BoujeeEnjinia1701/dustbadge/cad/drawings/DBG-DWG-001.pdf

CONCEPT, NOT FOR FABRICATION | DustBadge · github.com/BoujeeEnjinia1701/dustbadge

FRONT VIEW
Scale 1:1; looking at the front (along +Y)

TOP VIEW
Scale 1:1; looking down (along -Z)

RIGHT VIEW
Scale 1:1; looking at the right side (along -X)

64

35 52

6 ALERT LED LIGHT PIPE

5 MOTOR (HIDDEN)

3 SENSOR 41 x 41 x 12 (HIDDEN)

INLET | OUTLET

FRONT FACE (-Y), WORN FACING OUT

31
SHELL JOINT, GASKET

10 CLIP

AIR IN (DOWN)

ISOMETRIC VIEW
Not to scale; seen from the front right and above, about 30 deg elevation

MAIN DIMENSIONS AND INTERFACES (MM)
Shells 64 x 52 x 31; 35 deep with clip; wall 2; gasket 1 at 15 from the rear face Sensor SPS30 class 41 x 41 x 12, ports down onto two slots
Slots 12 x 7: inlet (screened) at X -19, outlet at X 1
USB-C opening at X 18; humidity vent at X 18; all in the bottom face
Cell 50 x 34 x 11.5, 2,000 mAh, protected, with thermistor; 13 foam pad 40 x 24 x 1 behind it Board 59 x 47 clamped by three M2 x 20 screws; TPU gasket and port seals
Mass 120.7 g (DBG-CAL-001); inlet 242 from nose and mouth when worn
Not intrinsically safe; not for gassy mines or explosive atmospheres
Wear shaded when ambient is above 40 °C in full sun
Third-angle; front view from -Y; origin at the badge center, rear face Y = 1
REV | DESCRIPTION | DATE | BY
P1 | Preliminary GA for TRL 3 (from cad/src/model.py) | 2026-09-25 | AC
P2 | 2,000 mAh cell, 11.5 thick; sun use rule (DBG-DDR-002) | 2026-09-25 | AC
P3 | Layout and labels tidied | 2026-09-25 | AC
P4 | Design for construction: screws, gasket, seals, ribs (DBG-DDR-003) | 2026-09-30 | AC
P5 | Worn version: rear 1 mm deeper, foam pad (DDR-003 A1) | 2026-10-02 | AC
DUSTBADGE | github.com/BoujeeEnjinia1701/dustbadge

## General arrangement

DRAWING NO.
DBG-DWG-001

REV
P5

SHEET
1 of 1

SIZE

## ANSI B

SCALE
1:1

UNITS
mm
PROJECTION | DATE
2026-10-02

DRAWN
Amish Chadha

MATERIAL / NOTES
PETG shells; bought-in parts per bom/bom.csv. PRELIMINARY, NOT FOR FABRICATION
Licensed CERN-OHL-S-2.0 · Design Molecule Lab · designmolecule.com | Generated from cad/src; do not edit by hand
