BoujeeEnjinia1701/dustbadge/cad/drawings/DBG-DWG-101.pdf

### BUILD PLAN SKETCH, PLAN NOT YET BUILT DustBadge · github.com/BoujeeEnjinia1701/dustbadge

FRONT VIEW
Scale 1:1; looking at the front (along +Y)

TOP VIEW
Scale 1:1; looking down (along -Z)

RIGHT VIEW
Scale 1:1; looking at the right side (along -X)

64

16 52

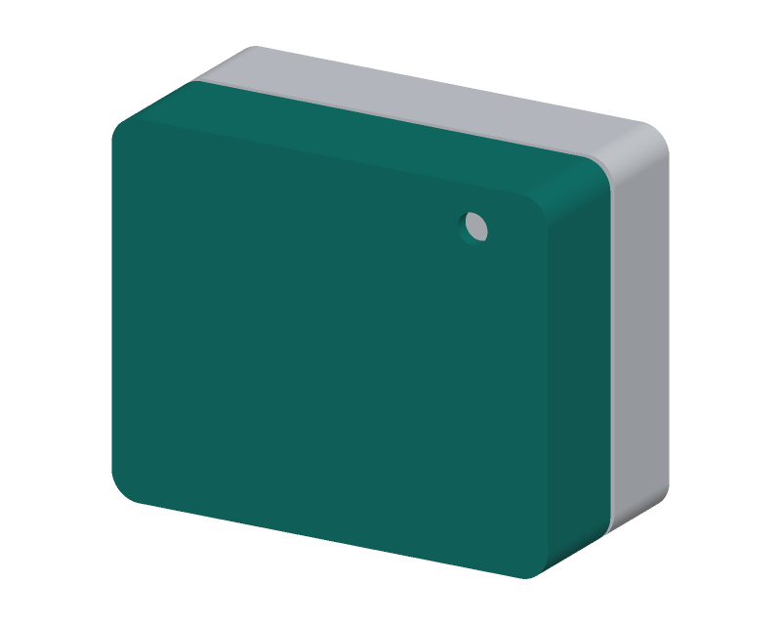
[picture p8: figure]

WHERE IT GOES
This part in colour, its neighbours in grey

HOW TO MAKE IT AND HOW IT FITS
Print face down (the front face on the bed); no supports needed. 64 x 52 x 16 mm, walls 2 mm, outside edges round 4 mm.
Bottom face openings (sideways from the centre line, + to the right seen from the front; depth from the front face):
inlet slot 12 x 7 at 19 left, outlet slot 12 x 7 at 1 right,
both 4.7 to 11.7 back; USB-C 9.6 x 3.8 at 18 right, 12.2 back; humidity vent 3 x 2 at 18.5 right, 2 to 4 back.
Light pipe hole 4.4 through the front face, 21 right, 20 above centre. Three screw bosses 5 dia, 14.2 long from the front face, at 27 left and 27 right 21 up, and 27 right 21 down: pilot hole 1.7 mm, 11 deep. Two stop ribs 1.2 thick above the sensor, 20 left and 2 right,
7 deep from the front face, their lower edge 0.2 above the sensor. Check: the sensor drops in under the ribs; the slots are clear.
REV | DESCRIPTION | DATE | BY
P1 | Making sketch for the prototype build plan | 2026-09-30 | AC
DUSTBADGE | github.com/BoujeeEnjinia1701/dustbadge

## DustBadge front shell: making sketch

DRAWING NO.
DBG-DWG-101

REV
P1

SHEET
1 of 1

SIZE

## ANSI B

SCALE
1:1

UNITS
mm
PROJECTION | DATE
2026-09-30

DRAWN
Amish Chadha

MATERIAL / NOTES
PETG, high-visibility yellow, 3D printed, 0.2 mm layers, 4 walls
Licensed CERN-OHL-S-2.0 · Design Molecule Lab · designmolecule.com | Generated from cad/src; do not edit by hand
