BoujeeEnjinia1701/dustbadge/cad/drawings/DBG-DWG-102.pdf

### BUILD PLAN SKETCH, PLAN NOT YET BUILT DustBadge · github.com/BoujeeEnjinia1701/dustbadge

FRONT VIEW
Scale 1:1; looking at the front (along +Y)

TOP VIEW
Scale 1:1; looking down (along -Z)

RIGHT VIEW
Scale 1:1; looking at the right side (along -X)

64

15 52

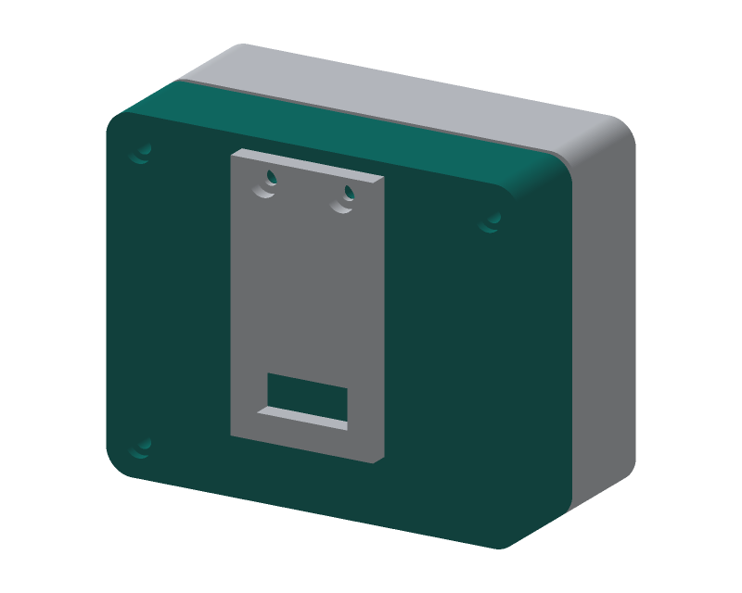
[picture p9: figure]

WHERE IT GOES
This part in colour, its neighbours in grey

HOW TO MAKE IT AND HOW IT FITS
Print rear face down; no supports needed.
64 x 52 x 14 mm, walls 2 mm, outside edges round 4 mm. Three tubes 4.5 dia, from the rear wall to 15.2 from the rear face, at the same places as the front bosses (seen from the front:
27 left and 27 right 21 up, 27 right 21 down); hole 2.4 through. Counterbore each from the rear face 4.2 dia, 1.4 deep (screw heads). Two clip bosses 5 dia, 5.5 long inside, 6 each side of centre,
21 up; pilot hole 1.7 mm, 7 deep from the rear face.
Four cell ribs 1.2 thick, 4 tall, 0.2 off the cell: two at the
sides (12 long), two at top and bottom (5 long).
Foam pad 40 x 24 x 1, stuck inside the back wall, centred. The rim is 14 from the rear face; the gasket sits on it. Check: the cell drops between the ribs and lifts out freely.
REV | DESCRIPTION | DATE | BY
P1 | Making sketch for the prototype build plan | 2026-09-30 | AC
DUSTBADGE | github.com/BoujeeEnjinia1701/dustbadge

## DustBadge rear shell: making sketch

DRAWING NO.
DBG-DWG-102

REV
P1

SHEET
1 of 1

SIZE

## ANSI B

SCALE
1:1

UNITS
mm
PROJECTION | DATE
2026-09-30

DRAWN
Amish Chadha

MATERIAL / NOTES
PETG, dark grey, 3D printed, 0.2 mm layers, 4 walls
Licensed CERN-OHL-S-2.0 · Design Molecule Lab · designmolecule.com | Generated from cad/src; do not edit by hand
