BoujeeEnjinia1701/dustbadge/cad/drawings/DBG-DWG-104.pdf

### BUILD PLAN SKETCH, PLAN NOT YET BUILT DustBadge · github.com/BoujeeEnjinia1701/dustbadge

FRONT VIEW
Scale 2:1; looking at the front (along +Y)

TOP VIEW
Scale 2:1; looking down (along -Z)

RIGHT VIEW
Scale 2:1; looking at the right side (along -X)

36

11 1

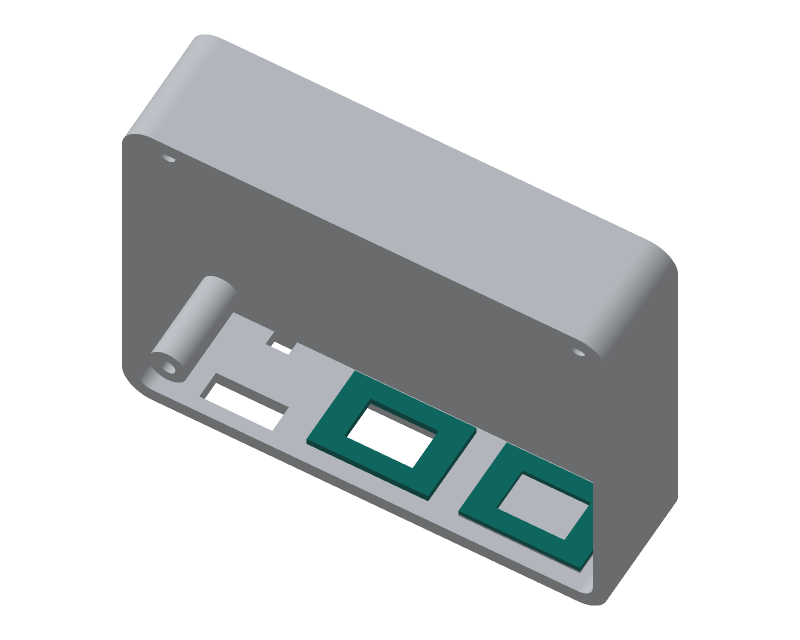
[picture p10: figure]

WHERE IT GOES
This part in colour, its neighbours in grey

HOW TO MAKE IT AND HOW IT FITS
Two flat seals, each 16 x 11 mm with a 9 x 6 mm opening in the middle that matches the sensor's inlet and outlet.
Inlet seal (left, sits on the screen): 0.7 mm thick.
Outlet seal (right, sits on the floor): 1.0 mm thick.
Print flat, slowly. Mark the inlet seal so they cannot be swapped. Fit: centre each over its slot on the inner floor, 18 mm apart centre to centre; a spot of adhesive holds it while assembling. The sensor rests on both seals, so they seal its ports to the slots and the fan draws only outside air.
Check: the sensor sits level on both seals.
REV | DESCRIPTION | DATE | BY
P1 | Making sketch for the prototype build plan | 2026-09-30 | AC
DUSTBADGE | github.com/BoujeeEnjinia1701/dustbadge

## DustBadge sensor port seals (make 2): making sketch

DRAWING NO.
DBG-DWG-104

REV
P1

SHEET
1 of 1

SIZE

## ANSI B

SCALE
2:1

UNITS
mm
PROJECTION | DATE
2026-09-30

DRAWN
Amish Chadha

MATERIAL / NOTES
TPU 95A, 3D printed, 100 % infill
Licensed CERN-OHL-S-2.0 · Design Molecule Lab · designmolecule.com | Generated from cad/src; do not edit by hand
