BoujeeEnjinia1701/dustbadge/cad/drawings/DBG-DWG-105.pdf

### BUILD PLAN SKETCH, PLAN NOT YET BUILT DustBadge · github.com/BoujeeEnjinia1701/dustbadge

FRONT VIEW
Scale 5:1; looking at the front (along +Y)

TOP VIEW
Scale 5:1; looking down (along -Z)

RIGHT VIEW
Scale 5:1; looking at the right side (along -X)

6

6 7

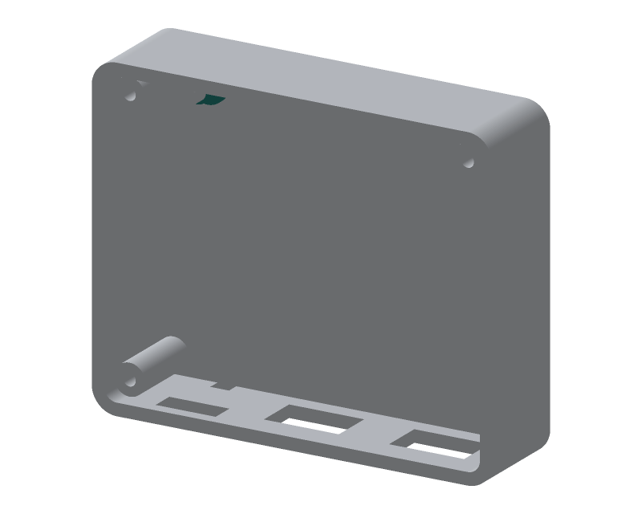
[picture p11: figure]

WHERE IT GOES
This part in colour, its neighbours in grey

HOW TO MAKE IT AND HOW IT FITS
A 4 mm rod 7 mm long with a 6 mm flange 1 mm thick, 3 mm from its outer end; a 3 mm pocket 2.5 deep in its inner end.
Print standing on its outer end, 100 % infill, so light runs along it. Fit: push it through the 4.4 mm hole from inside the front shell until the flange sits on the inner face; it stands 1 mm proud outside. A drop of clear adhesive on the flange holds it.
Push the 3 mm red LED into the pocket; a drop of adhesive. Check: the LED lit by a 3 V coin cell shows clearly outside.
REV | DESCRIPTION | DATE | BY
P1 | Making sketch for the prototype build plan | 2026-09-30 | AC
DUSTBADGE | github.com/BoujeeEnjinia1701/dustbadge

## DustBadge light pipe: making sketch

DRAWING NO.
DBG-DWG-105

REV
P1

SHEET
1 of 1

SIZE

## ANSI B

SCALE
5:1

UNITS
mm
PROJECTION | DATE
2026-09-30

DRAWN
Amish Chadha

MATERIAL / NOTES
Clear PETG, 3D printed, 100 % infill
Licensed CERN-OHL-S-2.0 · Design Molecule Lab · designmolecule.com | Generated from cad/src; do not edit by hand
