BoujeeEnjinia1701/dustbadge/cad/drawings/DBG-DWG-107.pdf

### BUILD PLAN SKETCH, PLAN NOT YET BUILT DustBadge · github.com/BoujeeEnjinia1701/dustbadge

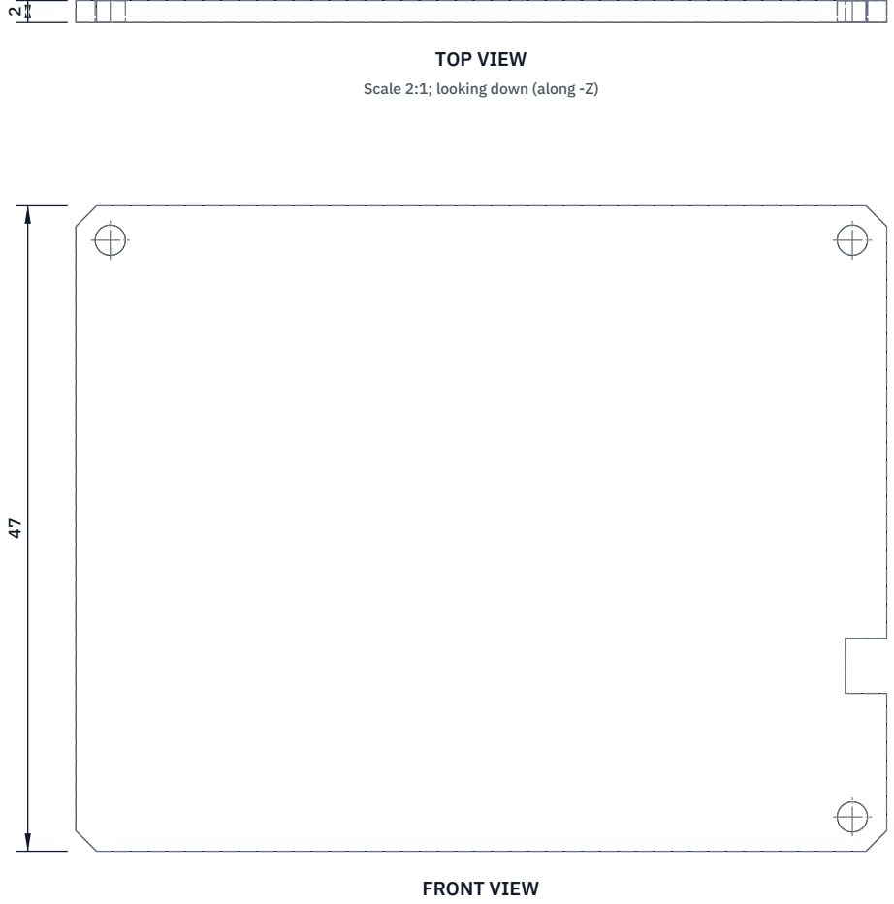
[picture p12: figure]
FRONT VIEW; TOP VIEW; Scale 2:1; looking down (along -Z)

Scale 2:1; looking at the front (along +Y)

RIGHT VIEW
Scale 2:1; looking at the right side (along -X)

59

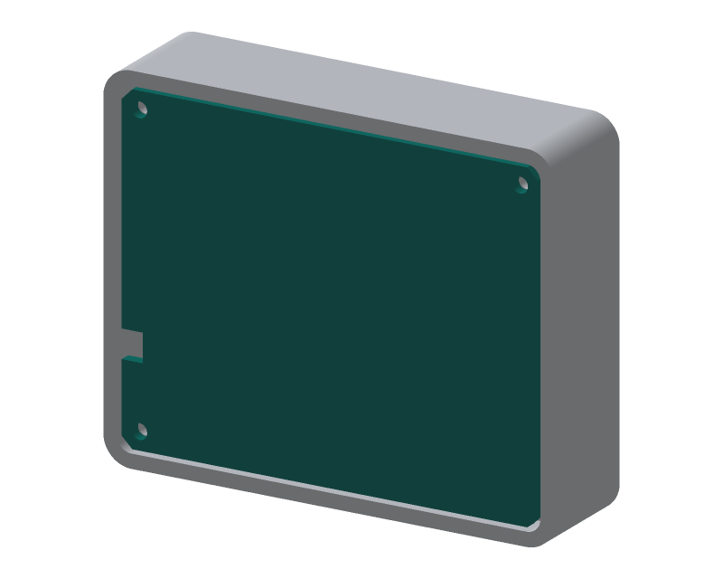
[picture p13: figure]

WHERE IT GOES
This part in colour, its neighbours in grey

HOW TO MAKE IT AND HOW IT FITS
Cut perfboard to 59 x 47 mm; file the edges straight and cut each corner off 1.5 mm at 45 degrees to clear the shell corners. Three 2.2 mm holes at the boss positions (seen from the front: 27 left and 27 right 21 up from the centre, 27 right 21 down). A notch 3 wide and 4 tall in the right edge, centred 10 below the centre, for the cell lead.
Front face (toward the sensor), right-hand strip: controller module on headers 12 to 30 right, 3.5 below to 17.5 above centre; charger module 12.6 to 23.6 right, from the bottom edge up 19 mm, its USB-C 1.2 below the bottom edge. The sensor's back rests on the left part of the front face. Check: the board sits flat on the three bosses.
REV | DESCRIPTION | DATE | BY
P1 | Making sketch for the prototype build plan | 2026-09-30 | AC
DUSTBADGE | github.com/BoujeeEnjinia1701/dustbadge

## DustBadge carrier board: making sketch

DRAWING NO.
DBG-DWG-107

REV
P1

SHEET
1 of 1

SIZE

## ANSI B

SCALE
2:1

UNITS
mm
PROJECTION | DATE
2026-09-30

DRAWN
Amish Chadha

MATERIAL / NOTES
Perfboard, 2.54 mm pitch, 1.6 mm FR4
Licensed CERN-OHL-S-2.0 · Design Molecule Lab · designmolecule.com | Generated from cad/src; do not edit by hand
