BoujeeEnjinia1701/dustbadge/cad/drawings/DBG-DWG-108.pdf

### BUILD PLAN SKETCH, PLAN NOT YET BUILT DustBadge · github.com/BoujeeEnjinia1701/dustbadge

FRONT VIEW
Scale 2:1; looking at the front (along +Y)

TOP VIEW
Scale 2:1; looking down (along -Z)

RIGHT VIEW
Scale 2:1; looking at the right side (along -X)

22

3 40

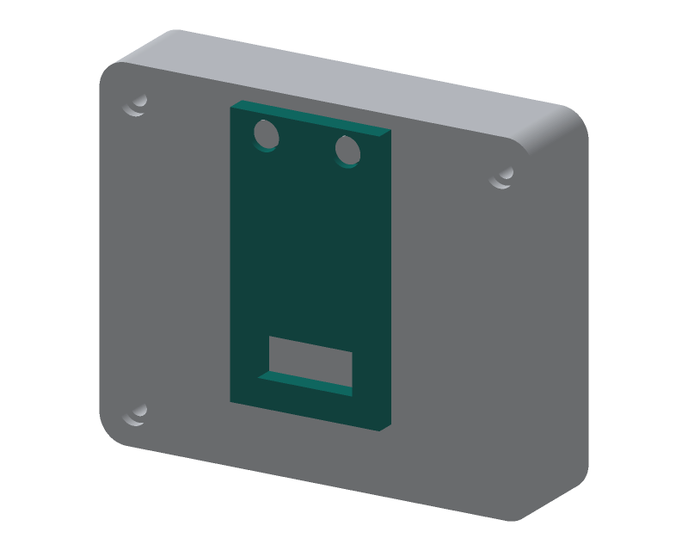
[picture p14: figure]

WHERE IT GOES
This part in colour, its neighbours in grey

HOW TO MAKE IT AND HOW IT FITS
A bought stainless spring clip with a strap loop, about 22 wide and 40 long, base leaf about 1 mm thick.
If its base leaf has no holes, drill two 2.2 mm holes 12 apart across the leaf, 3 mm from its top end; open the clip and
clamp the leaf on wood to drill; deburr.
Fit: base leaf flat on the rear face, centred, top end 2 mm below the badge's top edge; two M2 x 8 screws into the bosses. Check: the screw heads sit flat and the clip still closes.
REV | DESCRIPTION | DATE | BY
P1 | Making sketch for the prototype build plan | 2026-09-30 | AC
DUSTBADGE | github.com/BoujeeEnjinia1701/dustbadge

## DustBadge spring clip: drilling sketch

DRAWING NO.
DBG-DWG-108

REV
P1

SHEET
1 of 1

SIZE

## ANSI B

SCALE
2:1

UNITS
mm
PROJECTION | DATE
2026-09-30

DRAWN
Amish Chadha

MATERIAL / NOTES
Bought stainless spring clip, about 22 x 40 mm
Licensed CERN-OHL-S-2.0 · Design Molecule Lab · designmolecule.com | Generated from cad/src; do not edit by hand
