BoujeeEnjinia1701/dustbadge/media/card.png

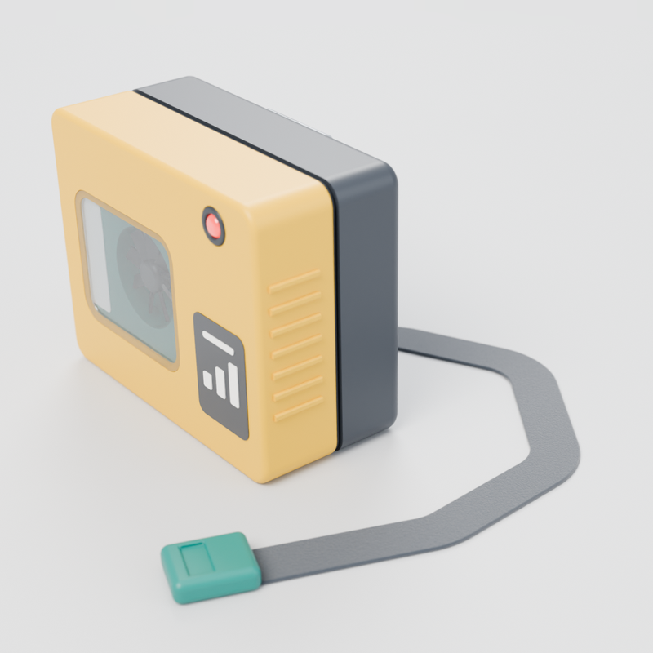
media/card.png
