BoujeeEnjinia1701/dustbadge/media/render-exploded.png

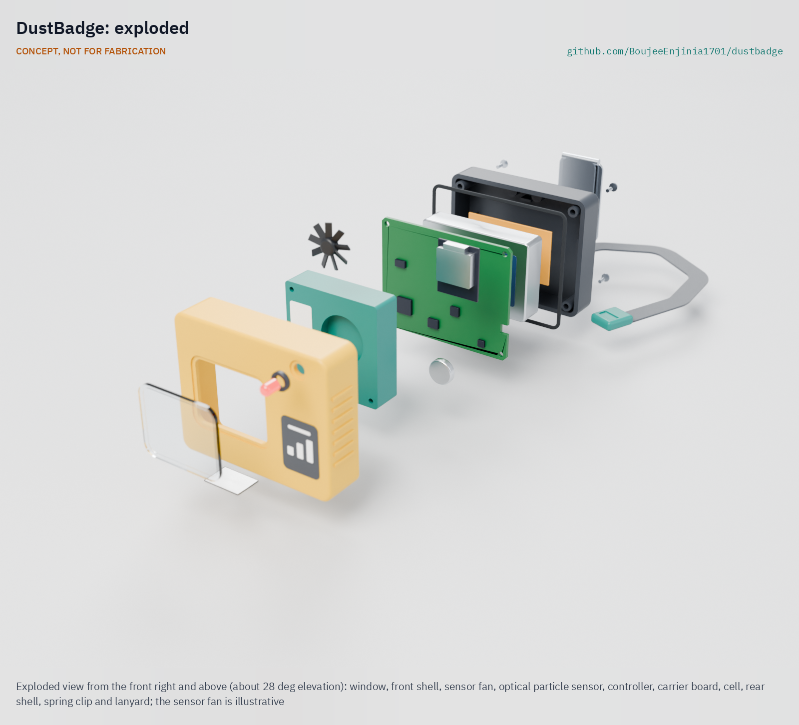
media/render-exploded.png
