BoujeeEnjinia1701/dustbadge/media/render-worn.png

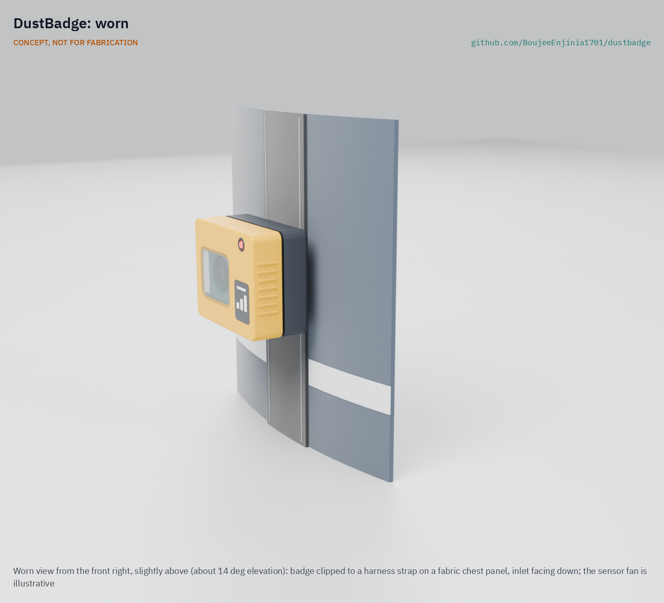
media/render-worn.png
