BoujeeEnjinia1701/dustbadge/media/social-preview.png

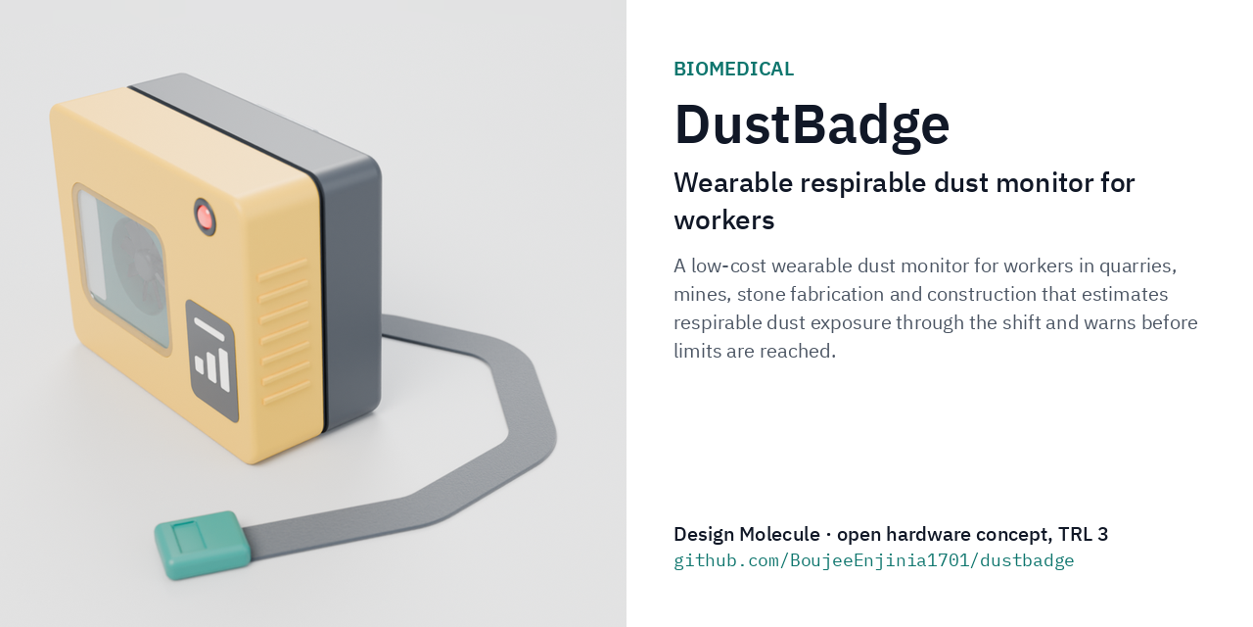
media/social-preview.png
